aeberbach/A1200KBv2/3dprint/Production/A1200net Light Pipe.stl

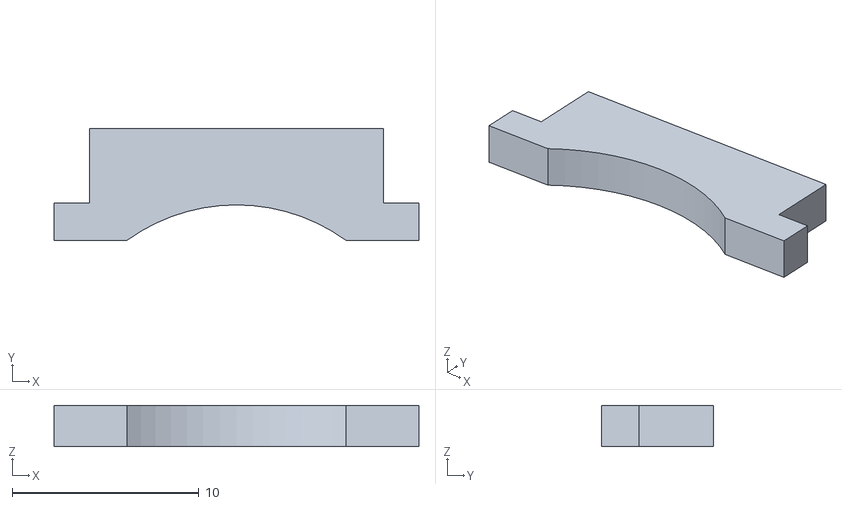
[picture p14: CAD file, 2024-08-07]
3dprint/Production/A1200net Light Pipe.stl
19.5 x 6.00 x 2.20
