aeberbach/A1200KBv2/3dprint/STEP/Lower mount.stl

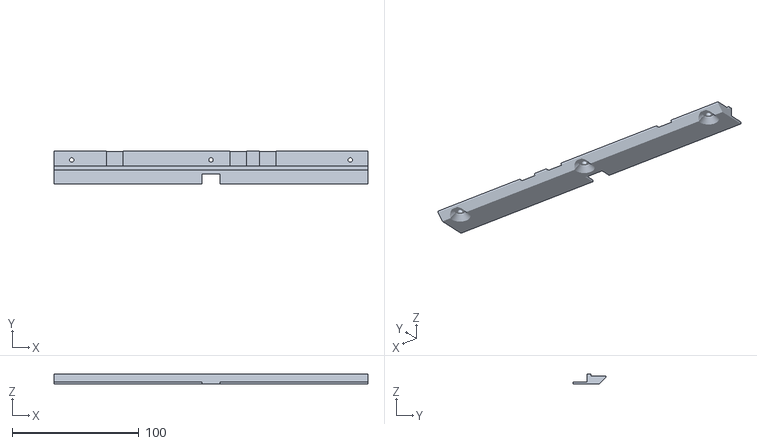
[picture p15: CAD file, 2025-01-12]
3dprint/STEP/Lower mount.stl
248.0 x 26.0 x 7.60
